parkertheplank/ECEN4024-SAM-Automation/ASAM_Schematic_Updated/SAM.kicad_sch

## KiCad design ASAM_Schematic_Updated/SAM.kicad_sch (2022-12-20, an earlier design)

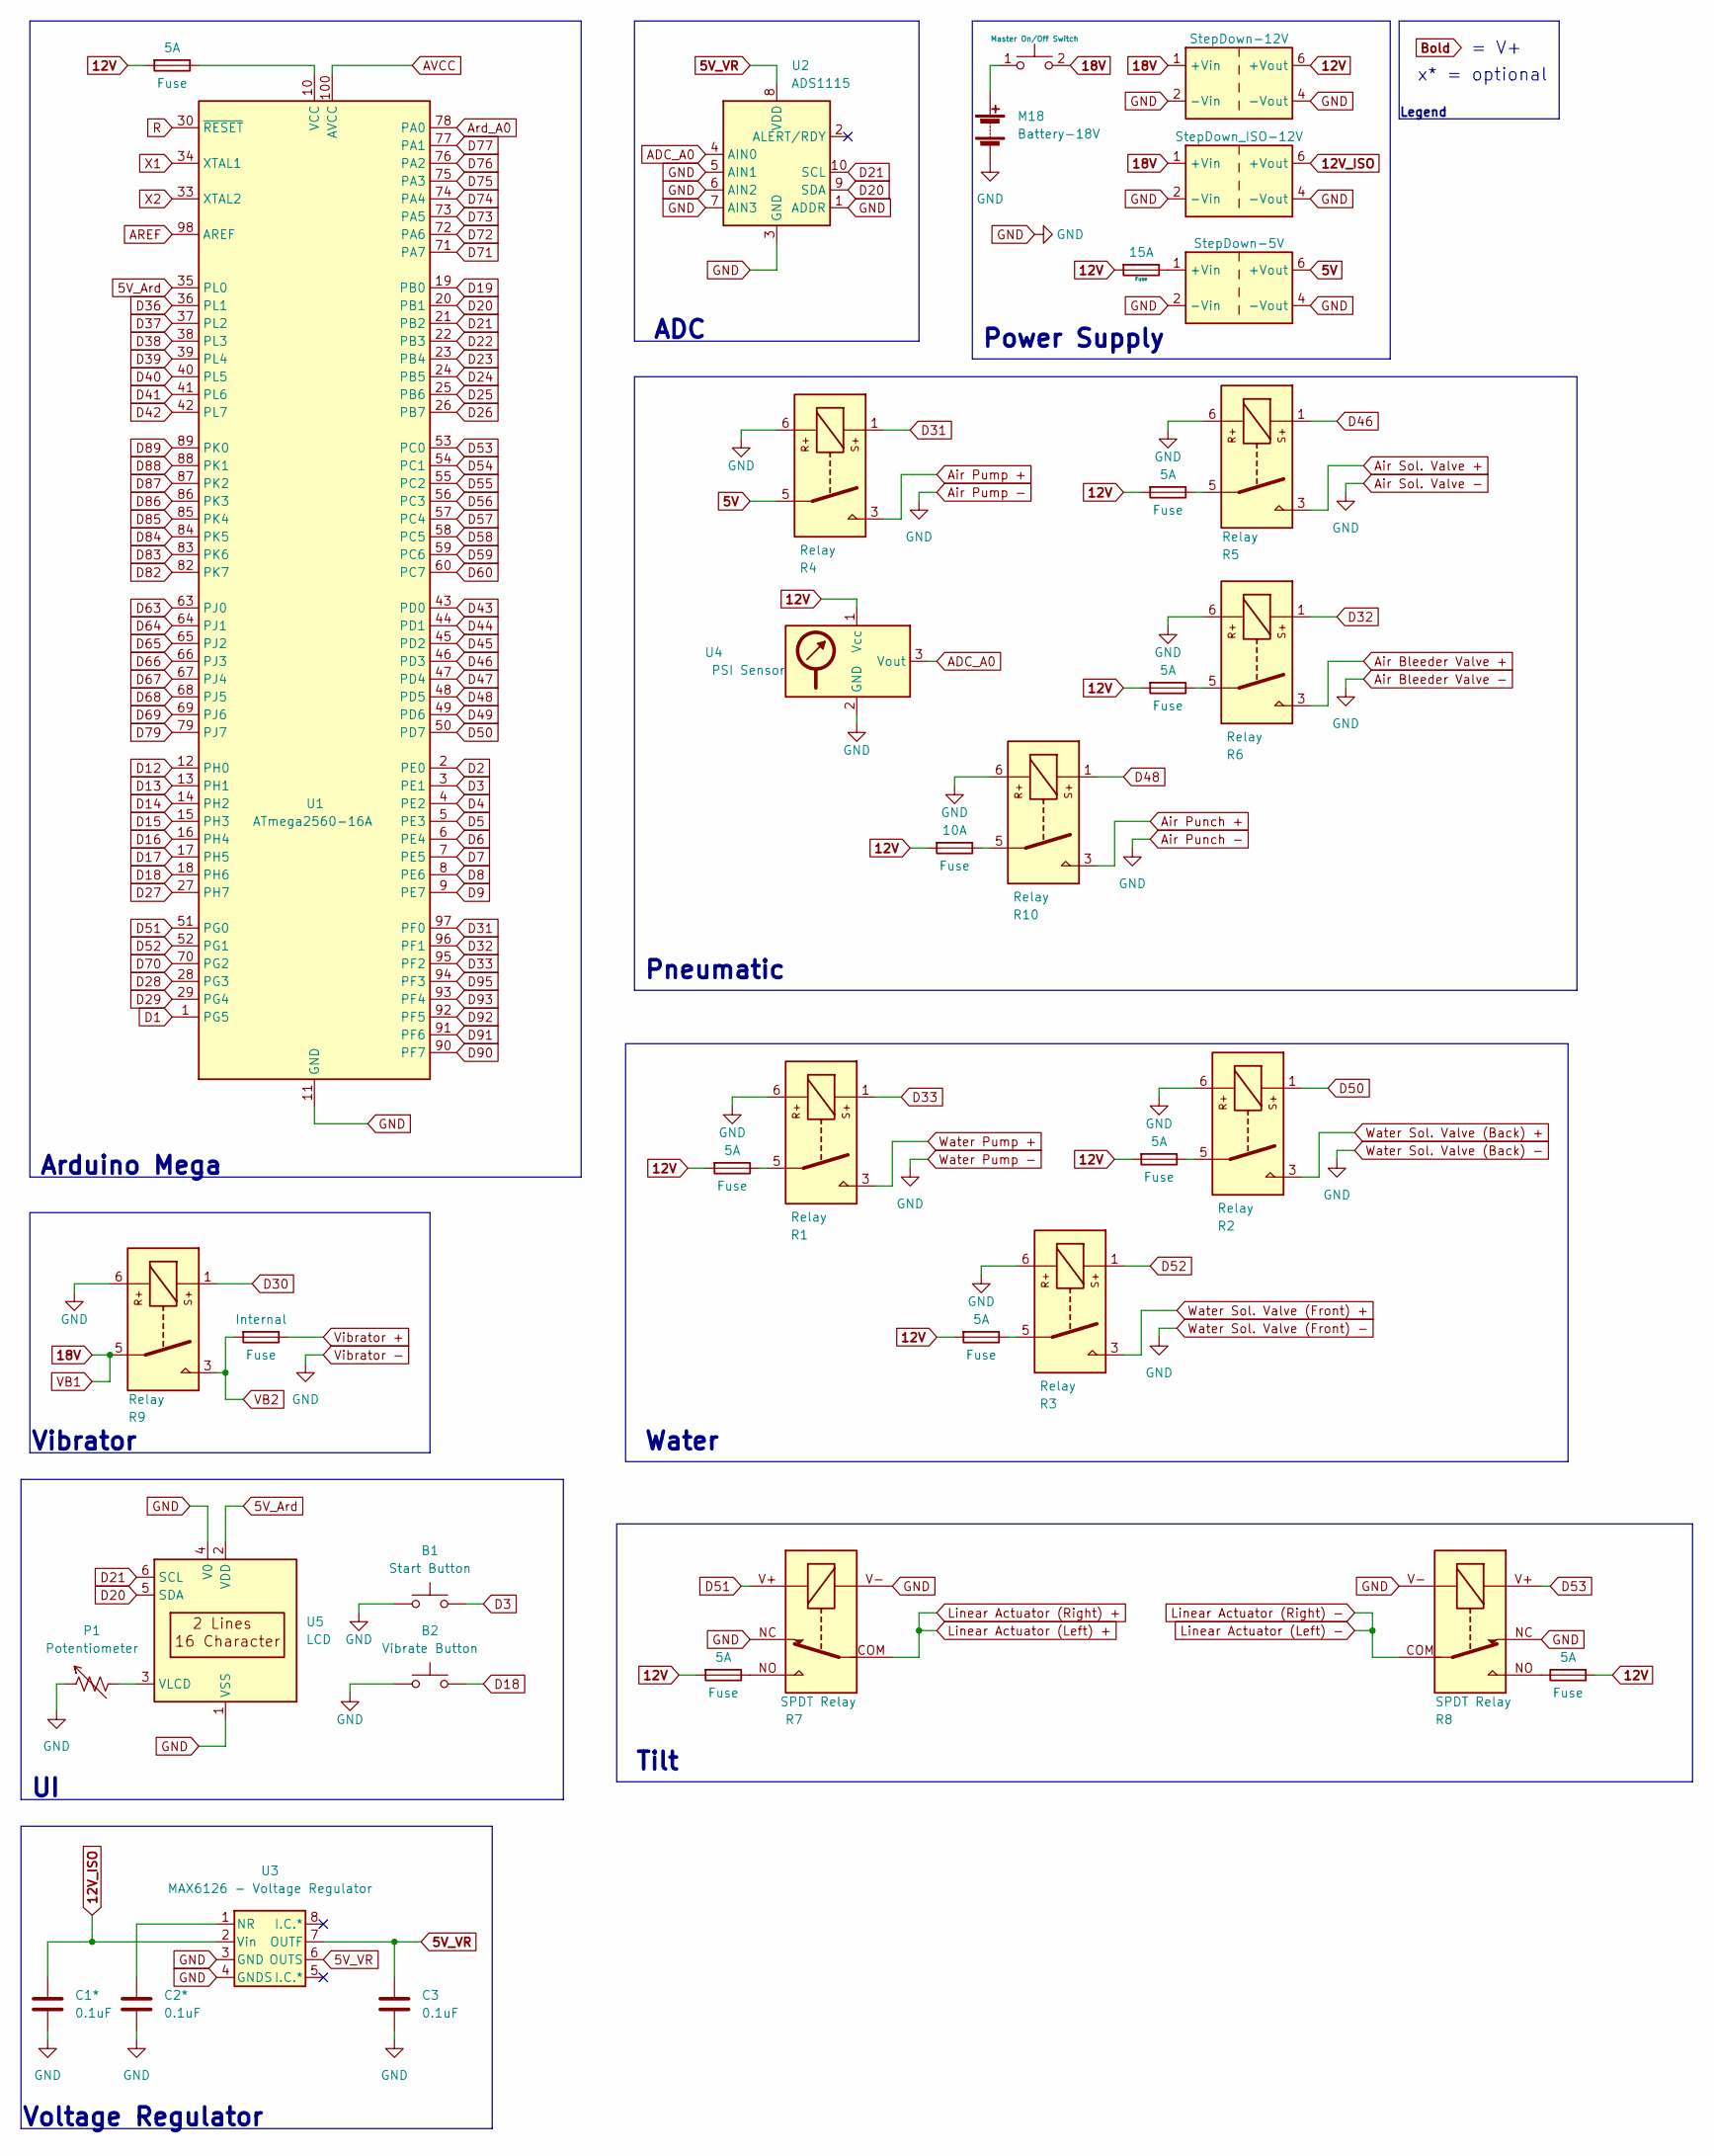
[picture p2: schematic SAM.kicad_sch]

Parts:
5A, 10A, 15A: Fuse
B1: Start Button
B2: Vibrate Button
C1*, C2*, C3: 0.1uF
Internal: Fuse
M18: Battery-18V
P1: Potentiometer
R1, R2, R3, R4, R5, R6, R9, R10: Relay; Relay_1P1T_NO_10x24x18.8mm_Panasonic_ADW11xxxxW_THT
R7, R8: SPDT Relay; Relay_SPDT_Finder_36.11
U1: ATmega2560-16A; TQFP-100_14x14mm_P0.5mm
U2: ADS1115; TSSOP-10_3x3mm_P0.5mm
U3: MAX6126 - Voltage Regulator; TO-252-2
U4: PSI Sensor
U5: LCD; EA_T123X-I2C

Connections:
5V: R4.5
5V_Ard: U1.35 (PL0), U5.2 (VDD)
5V_VR: C3.1, U2.8 (VDD), U3.6 (OUTS), U3.7 (OUTF)
12V: 5A.2, 10A.2, 15A.2, U4.1 (Vcc)
12V_ISO: C1*.1, U3.2 (Vin)
18V: R9.5
ADC_A0: U2.4 (AIN0), U4.3 (Vout)
AREF: U1.98 (AREF)
AVCC: U1.100 (AVCC)
Air Bleeder Valve +: R6.3
Air Pump +: R4.3
Air Punch +: R10.3
Air Sol. Valve +: R5.3
Ard_A0: U1.78 (PA0)
D1: U1.1 (PG5)
D2: U1.2 (PE0)
D3: B1.2, U1.3 (PE1)
D4: U1.4 (PE2)
D5: U1.5 (PE3)
D6: U1.6 (PE4)
D7: U1.7 (PE5)
D8: U1.8 (PE6)
D9: U1.9 (PE7)
D12: U1.12 (PH0)
D13: U1.13 (PH1)
D14: U1.14 (PH2)
D15: U1.15 (PH3)
D16: U1.16 (PH4)
D17: U1.17 (PH5)
D18: B2.2, U1.18 (PH6)
D19: U1.19 (PB0)
D20: U1.20 (PB1), U2.9 (SDA), U5.5 (SDA)
D21: U1.21 (PB2), U2.10 (SCL), U5.6 (SCL)
D22: U1.22 (PB3)
D23: U1.23 (PB4)
D24: U1.24 (PB5)
D25: U1.25 (PB6)
D26: U1.26 (PB7)
D27: U1.27 (PH7)
D28: U1.28 (PG3)
D29: U1.29 (PG4)
D30: R9.1
D31: R4.1, U1.97 (PF0)
D32: R6.1, U1.96 (PF1)
D33: R1.1, U1.95 (PF2)
D36: U1.36 (PL1)
D37: U1.37 (PL2)
D38: U1.38 (PL3)
D39: U1.39 (PL4)
D40: U1.40 (PL5)
D41: U1.41 (PL6)
D42: U1.42 (PL7)
D43: U1.43 (PD0)
D44: U1.44 (PD1)
D45: U1.45 (PD2)
D46: R5.1, U1.46 (PD3)
D47: U1.47 (PD4)
D48: R10.1, U1.48 (PD5)
D49: U1.49 (PD6)
D50: R2.1, U1.50 (PD7)
D51: R7.V+, U1.51 (PG0)
D52: R3.1, U1.52 (PG1)
D53: R8.V+, U1.53 (PC0)
D54: U1.54 (PC1)
D55: U1.55 (PC2)
D56: U1.56 (PC3)
D57: U1.57 (PC4)
D58: U1.58 (PC5)
D59: U1.59 (PC6)
D60: U1.60 (PC7)
D63: U1.63 (PJ0)
D64: U1.64 (PJ1)
D65: U1.65 (PJ2)
D66: U1.66 (PJ3)
D67: U1.67 (PJ4)
D68: U1.68 (PJ5)
D69: U1.69 (PJ6)
D70: U1.70 (PG2)
D71: U1.71 (PA7)
D72: U1.72 (PA6)
D73: U1.73 (PA5)
D74: U1.74 (PA4)
D75: U1.75 (PA3)
D76: U1.76 (PA2)
D77: U1.77 (PA1)
D79: U1.79 (PJ7)
D82: U1.82 (PK7)
D83: U1.83 (PK6)
D84: U1.84 (PK5)
D85: U1.85 (PK4)
D86: U1.86 (PK3)
D87: U1.87 (PK2)
D88: U1.88 (PK1)
D89: U1.89 (PK0)
D90: U1.90 (PF7)
D91: U1.91 (PF6)
D92: U1.92 (PF5)
D93: U1.93 (PF4)
D95: U1.94 (PF3)
GND: R7.NC, R7.V-, R8.NC, R8.V-, U1.11 (GND), U1.32 (GND), U1.62 (GND), U1.81 (GND), U1.99 (GND), U2.1 (ADDR), U2.3 (GND), U2.5 (AIN1), U2.6 (AIN2), U2.7 (AIN3), U3.3 (GND), U3.4 (GNDS), U5.1 (VSS), U5.4 (V0)
Linear Actuator (Left) +: R7.COM
Linear Actuator (Left) -: R8.COM
unnamed: 5A.1, R1.5, R2.5, R3.5, R5.5, R6.5, R7.NO, R8.NO, U1.10 (VCC), U1.31 (VCC), U1.61 (VCC), U1.80 (VCC)
unnamed: 10A.1, R10.5
unnamed: C2*.1, U3.1 (NR)
unnamed: P1.2, U5.3 (VLCD)
R: U1.30 (~RESET)
VB2: Internal.2, R9.3
Vibrator +: Internal.1
Water Pump +: R1.3
Water Sol. Valve (Back) +: R2.3
Water Sol. Valve (Front) +: R3.3
X1: U1.34 (XTAL1)
X2: U1.33 (XTAL2)

Notes on the sheet:
Voltage Regulator
Legend
Vibrator
Pneumatic
Water
ADC
Arduino Mega
Power Supply
x* = optional
Tilt
= V+
