parkertheplank/ECEN4024-SAM-Automation/SAM-KICAD-Schematic/SAM-Schematic.kicad_sch

## KiCad design SAM-KICAD-Schematic/SAM-Schematic.kicad_sch (2022-09-09)

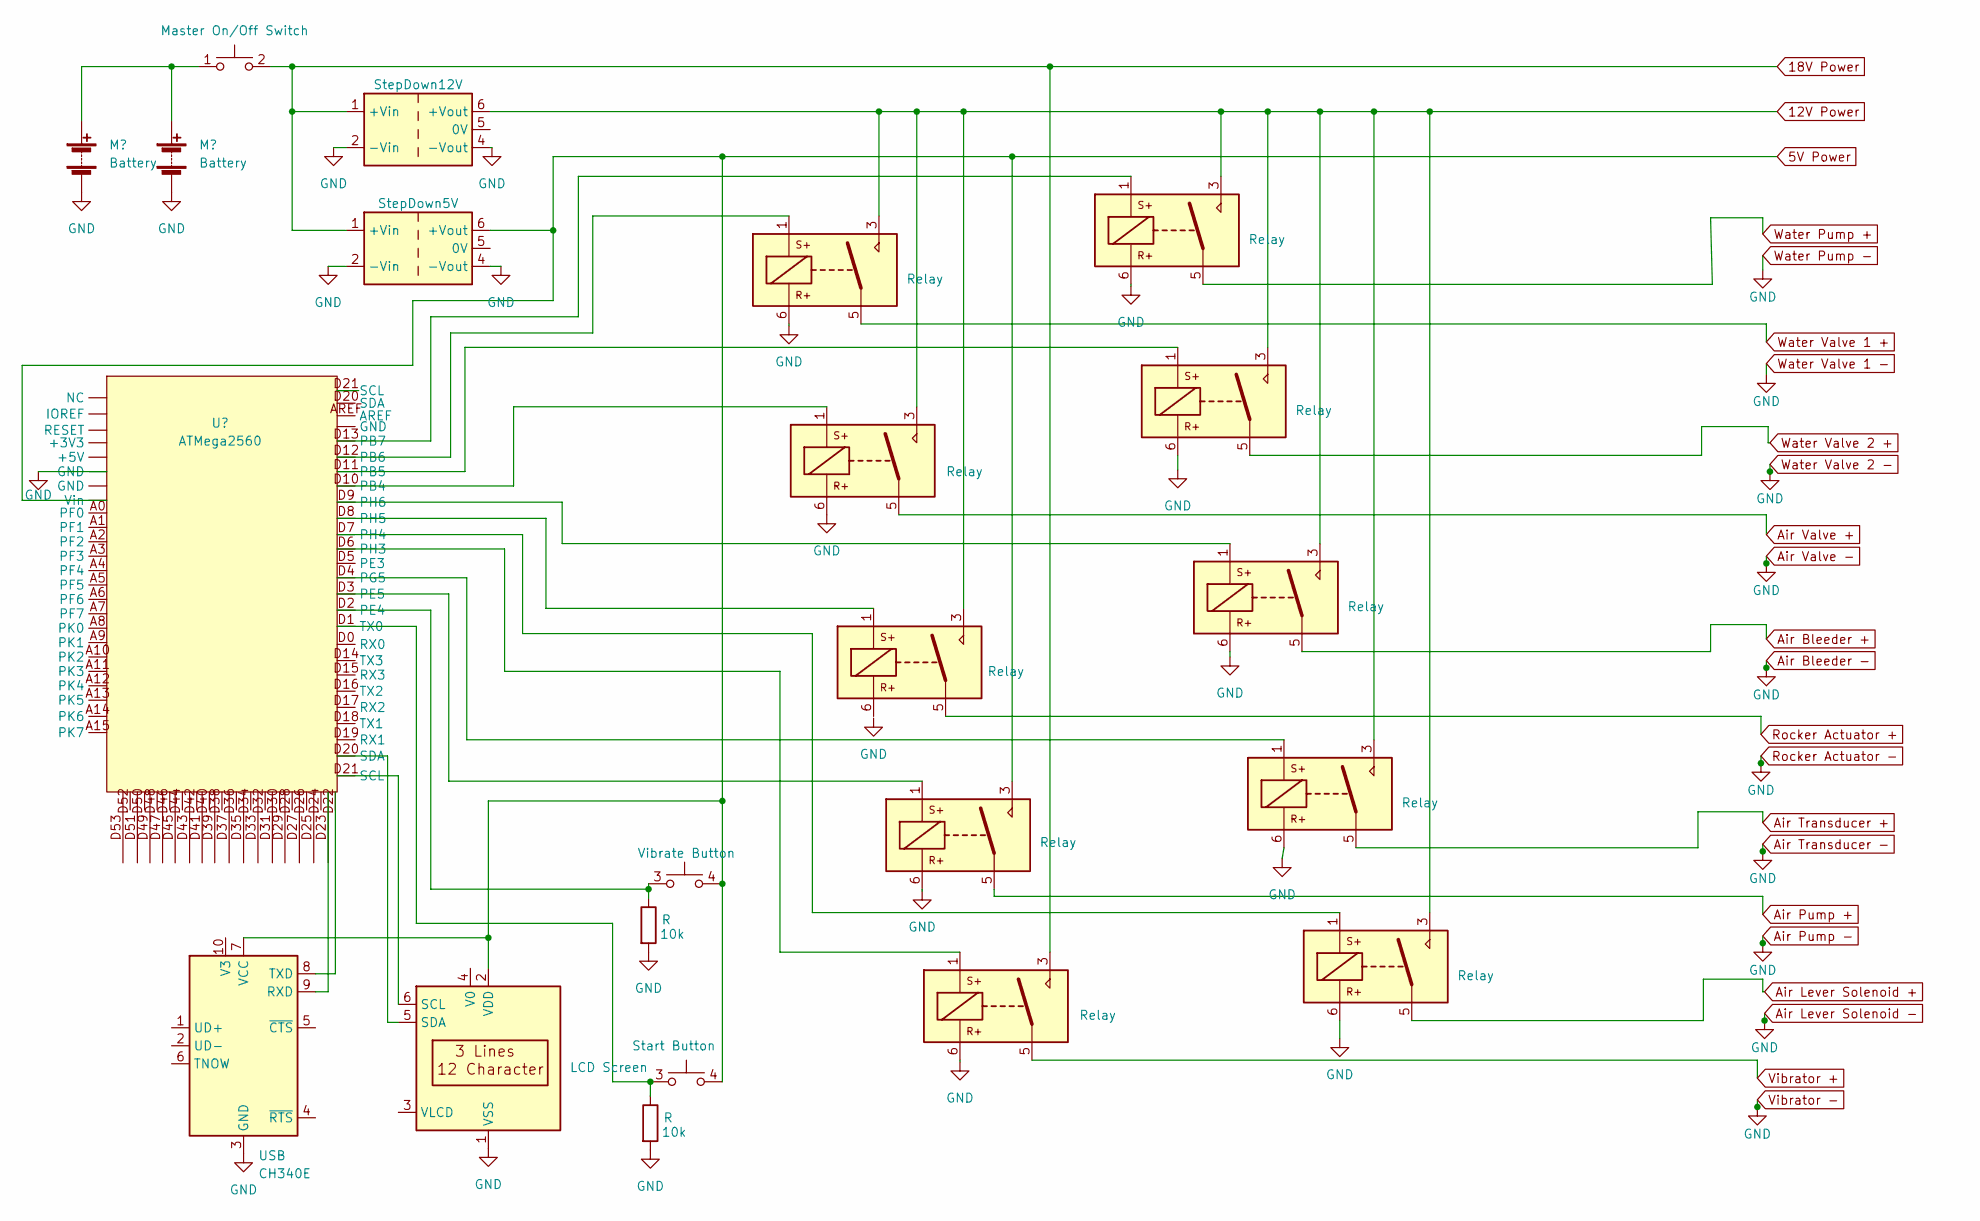
[picture p3: schematic SAM-Schematic.kicad_sch]

Parts:
10k: R
USB: CH340E; MSOP-10_3x3mm_P0.5mm

Connections:
5V Power: USB.7 (VCC)
