parkertheplank/ECEN4024-SAM-Automation/masterSAM/mechanical.ino

void mechSetup()
{
  pinMode(vib, OUTPUT);
  pinMode(tilt1, OUTPUT);
  pinMode(tilt2, OUTPUT);
  
  digitalWrite(vib, off);  
  digitalWrite(tilt1, off); 
  digitalWrite(tilt2, off);
}

void tilt(int state)
{
  digitalWrite(tilt1, state); //must be invvers or fuse will blow
  digitalWrite(tilt2, !state);  
  delay(9500); //Time derived by ten trial bubble tilt testing
  digitalWrite(tilt1, off);
  digitalWrite(tilt2, off);  
} 

void vibrate(int state) { digitalWrite(vib, state); }
