parkertheplank/ECEN4024-SAM-Automation/masterSAM/water.ino

void waterSetup() 
{
  pinMode(waterPump, OUTPUT);
  pinMode(waterValveIn, OUTPUT);
  pinMode(waterValveOut, OUTPUT);
  
  digitalWrite(waterValveIn, off);
  digitalWrite(waterValveOut, off);
  digitalWrite(waterPump, off);
  
  waterClose();
}

void waterFill(bool second) 
{
  digitalWrite(waterValveOut, on);
  if (second) //time depressurize after second interation
  {
    delay(4000);
    airEqualize(on);
    delay(3000);
    delayAndUpdate(50, 2000);
    airEqualize(off);
    lcdPrint(waterFlag);
  }
  digitalWrite(waterValveIn, on);
  digitalWrite(waterPump, on);
} 

void waterClose()
{
  digitalWrite(waterPump, off);
  digitalWrite(waterValveIn, off);
  delay(500);
  digitalWrite(waterValveOut, off);
} 
