parkertheplank/ECEN4024-SAM-Automation/LCD1602_SAMMENU/LCD1602_SAMMENU/LiquidMenu_debug.h

/**
@file
Contains debug macro definitions for LiquidMenu library.
*/


#pragma once

#if LIQUIDMENU_DEBUG
  #ifdef ARDUINO_ARCH_AVR
    #include <Arduino.h>
    #define DEBUG(x) Serial.print(x);
    #define DEBUGLN(x) Serial.println(x);
    #define DEBUG2(x, y) Serial.print(x, y);
    #define DEBUGLN2(x, y) Serial.println(x, y);
  #else
    #define DEBUG(x) std::cout << x;
    #define DEBUGLN(x) std::cout << x << std::endl;
    #define DEBUG2(x, y) std::cout << x << y;
    #define DEBUGLN2(x, y) std::cout << x << y << std::endl;
  #endif
#else
  /// Debug print
  #define DEBUG(x)
  /// Debug print with newline
  #define DEBUGLN(x)
  /// Debug print two parameters
  #define DEBUG2(x, y)
  /// Debug print two parameters with newline
  #define DEBUGLN2(x, y)
#endif
